Puzzlers100/USBC-eDP-DriverBoard/Software/USBPD/App/usbpd_pdo_defs.h

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

#ifndef __USBPD_PDO_DEF_H_
#define __USBPD_PDO_DEF_H_

#ifdef __cplusplus
 extern "C" {
#endif

/* Includes ------------------------------------------------------------------*/
#include "usbpd_def.h"

/* Define   ------------------------------------------------------------------*/
#define PORT0_NB_SOURCEPDO         0U   /* Number of Source PDOs (applicable for port 0)   */
#define PORT0_NB_SINKPDO           1U   /* Number of Sink PDOs (applicable for port 0)     */
/* Exported typedef ----------------------------------------------------------*/
/* USER CODE BEGIN typedef */
/**
  * @brief  USBPD Port PDO Structure definition
  *
  */
/* USER CODE END typedef */

/* Exported define -----------------------------------------------------------*/
/* USER CODE BEGIN Exported_Define */

#define USBPD_CORE_PDO_SRC_FIXED_MAX_CURRENT 3
#define USBPD_CORE_PDO_SNK_FIXED_MAX_CURRENT 1500

/* USER CODE END Exported_Define */

/* Exported constants --------------------------------------------------------*/

/* Exported macro ------------------------------------------------------------*/

/* Exported variables --------------------------------------------------------*/
#ifndef __USBPD_PWR_IF_C
extern uint32_t PORT0_PDO_ListSRC[USBPD_MAX_NB_PDO];
extern uint32_t PORT0_PDO_ListSNK[USBPD_MAX_NB_PDO];
#else
/* Definition of Source PDO for Port 0 */
uint32_t PORT0_PDO_ListSRC[USBPD_MAX_NB_PDO] =
{
  /* PDO 1 */ (0x00000000U),
  /* PDO 2 */ (0x00000000U),
  /* PDO 3 */ (0x00000000U),
  /* PDO 4 */ (0x00000000U),
  /* PDO 5 */ (0x00000000U),
  /* PDO 6 */ (0x00000000U),
  /* PDO 7 */ (0x00000000U),
};

/* Definition of Sink PDO for Port 0 */
uint32_t PORT0_PDO_ListSNK[USBPD_MAX_NB_PDO] =
{
  /* PDO 1 */
  (
    USBPD_PDO_TYPE_FIXED                 | /* Fixed supply PDO            */

    USBPD_PDO_SNK_FIXED_SET_VOLTAGE(5000U)         | /* Voltage in mV               */
    USBPD_PDO_SNK_FIXED_SET_OP_CURRENT(3000U)     | /* Operating current in  mA            */

    /* Common definitions applicable to all PDOs, defined only in PDO 1 */
    USBPD_PDO_SNK_FIXED_FRS_NOT_SUPPORTED          | /* Fast Role Swap				 */
    USBPD_PDO_SNK_FIXED_DRD_SUPPORTED          | /* Dual-Role Data              */
    USBPD_PDO_SNK_FIXED_USBCOMM_NOT_SUPPORTED      | /* USB Communications          */
    USBPD_PDO_SNK_FIXED_EXT_POWER_NOT_AVAILABLE    | /* External Power              */
    USBPD_PDO_SNK_FIXED_HIGHERCAPAB_NOT_SUPPORTED   | /* Higher Capability           */
    USBPD_PDO_SNK_FIXED_DRP_NOT_SUPPORTED            /* Dual-Role Power             */
  ),
  /* PDO 2 */ (0x00000000U),
  /* PDO 3 */ (0x00000000U),
  /* PDO 4 */ (0x00000000U),
  /* PDO 5 */ (0x00000000U),
  /* PDO 6 */ (0x00000000U),
  /* PDO 7 */ (0x00000000U),
};

#endif

/* Exported functions --------------------------------------------------------*/

#ifdef __cplusplus
}
#endif

#endif /* __USBPD_PDO_DEF_H_ */
